pmacinec/programmer-reminder-arduino/src/main/icons.h

/**
 * Made with Marlin Bitmap Converter
 * http://marlinfw.org/tools/u8glib/converter.html
 */

const unsigned char temperatureBitmap [] PROGMEM = {
  0x03, 0x00,
  0x07, 0xF0,
  0x04, 0xE0,
  0x04, 0x80,
  0x04, 0xC0,
  0x04, 0xF0,
  0x04, 0x80,
  0x04, 0xE0,
  0x04, 0xC0,
  0x07, 0xF0,
  0x07, 0x80,
  0x07, 0x80,
  0x0F, 0xC0,
  0x0F, 0xC0,
  0x0F, 0xC0,
  0x07, 0x80
};

const unsigned char humidityBitmap [] PROGMEM = {
  0x01, 0x00,
  0x01, 0x80,
  0x03, 0xC0,
  0x06, 0x60,
  0x06, 0x60,
  0x0C, 0x30,
  0x18, 0x38,
  0x18, 0x18,
  0x38, 0x18,
  0x38, 0x1C,
  0x30, 0x0C,
  0x38, 0x1C,
  0x18, 0x18,
  0x1C, 0x38,
  0x0E, 0xF0,
  0x03, 0xC0
};

const unsigned char illuminanceBitmap [] PROGMEM = {
  0x00, 0x00,
  0x09, 0x90,
  0x0D, 0xB0,
  0x04, 0x20,
  0x63, 0xC6,
  0x34, 0x2C,
  0x08, 0x10,
  0x68, 0x16,
  0x68, 0x16,
  0x08, 0x10,
  0x34, 0x2C,
  0x63, 0xC6,
  0x04, 0x20,
  0x0D, 0xB0,
  0x09, 0x90,
  0x00, 0x00
};
